bcamellia/Serial-Mini/Firmware/config.h

/* Microchip Technology Inc. and its subsidiaries.  You may use this software 
 * and any derivatives exclusively with Microchip products. 
 * 
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
 * IN NO EVENT WILL MICROCHIP BE LIABLE FOR ANY INDIRECT, SPECIAL, PUNITIVE, 
 * INCIDENTAL OR CONSEQUENTIAL LOSS, DAMAGE, COST OR EXPENSE OF ANY KIND 
 * WHATSOEVER RELATED TO THE SOFTWARE, HOWEVER CAUSED, EVEN IF MICROCHIP HAS 
 * BEEN ADVISED OF THE POSSIBILITY OR THE DAMAGES ARE FORESEEABLE.  TO THE 
 * FULLEST EXTENT ALLOWED BY LAW, MICROCHIP'S TOTAL LIABILITY ON ALL CLAIMS 
 * IN ANY WAY RELATED TO THIS SOFTWARE WILL NOT EXCEED THE AMOUNT OF FEES, IF 
 * ANY, THAT YOU HAVE PAID DIRECTLY TO MICROCHIP FOR THIS SOFTWARE.
 *
 * MICROCHIP PROVIDES THIS SOFTWARE CONDITIONALLY UPON YOUR ACCEPTANCE OF THESE 
 * TERMS. 
 */

/* 
 * File:   
 * Author: 
 * Comments:
 * Revision history: 
 */

// This is a guard condition so that contents of this file are not included
// more than once.  
#ifndef XC_HEADER_TEMPLATE_H
#define	XC_HEADER_TEMPLATE_H


// DSPIC33CK32MP102 Configuration Bit Settings

// 'C' source line config statements

// FSEC
#pragma config BWRP = OFF               // Boot Segment Write-Protect bit (Boot Segment may be written)
#pragma config BSS = DISABLED           // Boot Segment Code-Protect Level bits (No Protection (other than BWRP))
#pragma config BSEN = OFF               // Boot Segment Control bit (No Boot Segment)
#pragma config GWRP = OFF               // General Segment Write-Protect bit (General Segment may be written)
#pragma config GSS = DISABLED           // General Segment Code-Protect Level bits (No Protection (other than GWRP))
#pragma config CWRP = OFF               // Configuration Segment Write-Protect bit (Configuration Segment may be written)
#pragma config CSS = DISABLED           // Configuration Segment Code-Protect Level bits (No Protection (other than CWRP))
#pragma config AIVTDIS = OFF            // Alternate Interrupt Vector Table bit (Disabled AIVT)

// FBSLIM
#pragma config BSLIM = 0x1FFF           // Boot Segment Flash Page Address Limit bits (Enter Hexadecimal value)

// FOSCSEL
#pragma config FNOSC = FRCDIVN          // Oscillator Source Selection (Internal Fast RC (FRC) Oscillator with postscaler)
#pragma config IESO = OFF               // Two-speed Oscillator Start-up Enable bit (Start up with user-selected oscillator source)

// FOSC
#pragma config POSCMD = NONE            // Primary Oscillator Mode Select bits (Primary Oscillator disabled)
#pragma config OSCIOFNC = ON            // OSC2 Pin Function bit (OSC2 is general purpose digital I/O pin)
#pragma config FCKSM = CSDCMD           // Clock Switching Mode bits (Both Clock switching and Fail-safe Clock Monitor are disabled)
#pragma config PLLKEN = ON              // PLL Lock Enable (PLL clock output will be disabled if LOCK is lost)
#pragma config XTCFG = G3               // XT Config (24-32 MHz crystals)
#pragma config XTBST = ENABLE           // XT Boost (Boost the kick-start)

// FWDT
#pragma config RWDTPS = PS2147483648    // Run Mode Watchdog Timer Post Scaler select bits (1:2147483648)
#pragma config RCLKSEL = LPRC           // Watchdog Timer Clock Select bits (Always use LPRC)
#pragma config WINDIS = OFF             // Watchdog Timer Window Enable bit (Watchdog Timer operates in Window mode)
#pragma config WDTWIN = WIN25           // Watchdog Timer Window Select bits (WDT Window is 25% of WDT period)
#pragma config SWDTPS = PS2147483648    // Sleep Mode Watchdog Timer Post Scaler select bits (1:2147483648)
#pragma config FWDTEN = ON_SW           // Watchdog Timer Enable bit (WDT controlled via SW, use WDTCON.ON bit)

// FPOR
#pragma config BISTDIS = DISABLED       // Memory BIST Feature Disable (mBIST on reset feature disabled)

// FICD
#pragma config ICS = PGD1               // ICD Communication Channel Select bits (Communicate on PGC1 and PGD1)
#pragma config JTAGEN = OFF             // JTAG Enable bit (JTAG is disabled)

// FDMTIVTL
#pragma config DMTIVTL = 0x0            // Dead Man Timer Interval low word (Enter Hexadecimal value)

// FDMTIVTH
#pragma config DMTIVTH = 0x0            // Dead Man Timer Interval high word (Enter Hexadecimal value)

// FDMTCNTL
#pragma config DMTCNTL = 0x0            // Lower 16 bits of 32 bit DMT instruction count time-out value (0-0xFFFF) (Enter Hexadecimal value)

// FDMTCNTH
#pragma config DMTCNTH = 0x0            // Upper 16 bits of 32 bit DMT instruction count time-out value (0-0xFFFF) (Enter Hexadecimal value)

// FDMT
#pragma config DMTDIS = OFF             // Dead Man Timer Disable bit (Dead Man Timer is Disabled and can be enabled by software)

// FDEVOPT
#pragma config ALTI2C1 = OFF            // Alternate I2C1 Pin bit (I2C1 mapped to SDA1/SCL1 pins)
#pragma config ALTI2C2 = OFF            // Alternate I2C2 Pin bit (I2C2 mapped to SDA2/SCL2 pins)
#pragma config SMB3EN = SMBUS3          // SM Bus Enable (SMBus 3.0 input levels)
#pragma config SPI2PIN = PPS            // SPI2 Pin Select bit (SPI2 uses I/O remap (PPS) pins)

// FALTREG
#pragma config CTXT1 = OFF              // Specifies Interrupt Priority Level (IPL) Associated to Alternate Working Register 1 bits (Not Assigned)
#pragma config CTXT2 = OFF              // Specifies Interrupt Priority Level (IPL) Associated to Alternate Working Register 2 bits (Not Assigned)
#pragma config CTXT3 = OFF              // Specifies Interrupt Priority Level (IPL) Associated to Alternate Working Register 3 bits (Not Assigned)
#pragma config CTXT4 = OFF              // Specifies Interrupt Priority Level (IPL) Associated to Alternate Working Register 4 bits (Not Assigned)

// #pragma config statements should precede project file includes.
// Use project enums instead of #define for ON and OFF.

#include <xc.h>



/**
 * @param void
 * @return 0
 */
int main(void);


#endif	/* XC_HEADER_TEMPLATE_H */
